daveho/FPGA_VGA/Schematic/FPGA_VGA.kicad_sch

## KiCad design Schematic/FPGA_VGA.kicad_sch (2025-11-19, an earlier design)

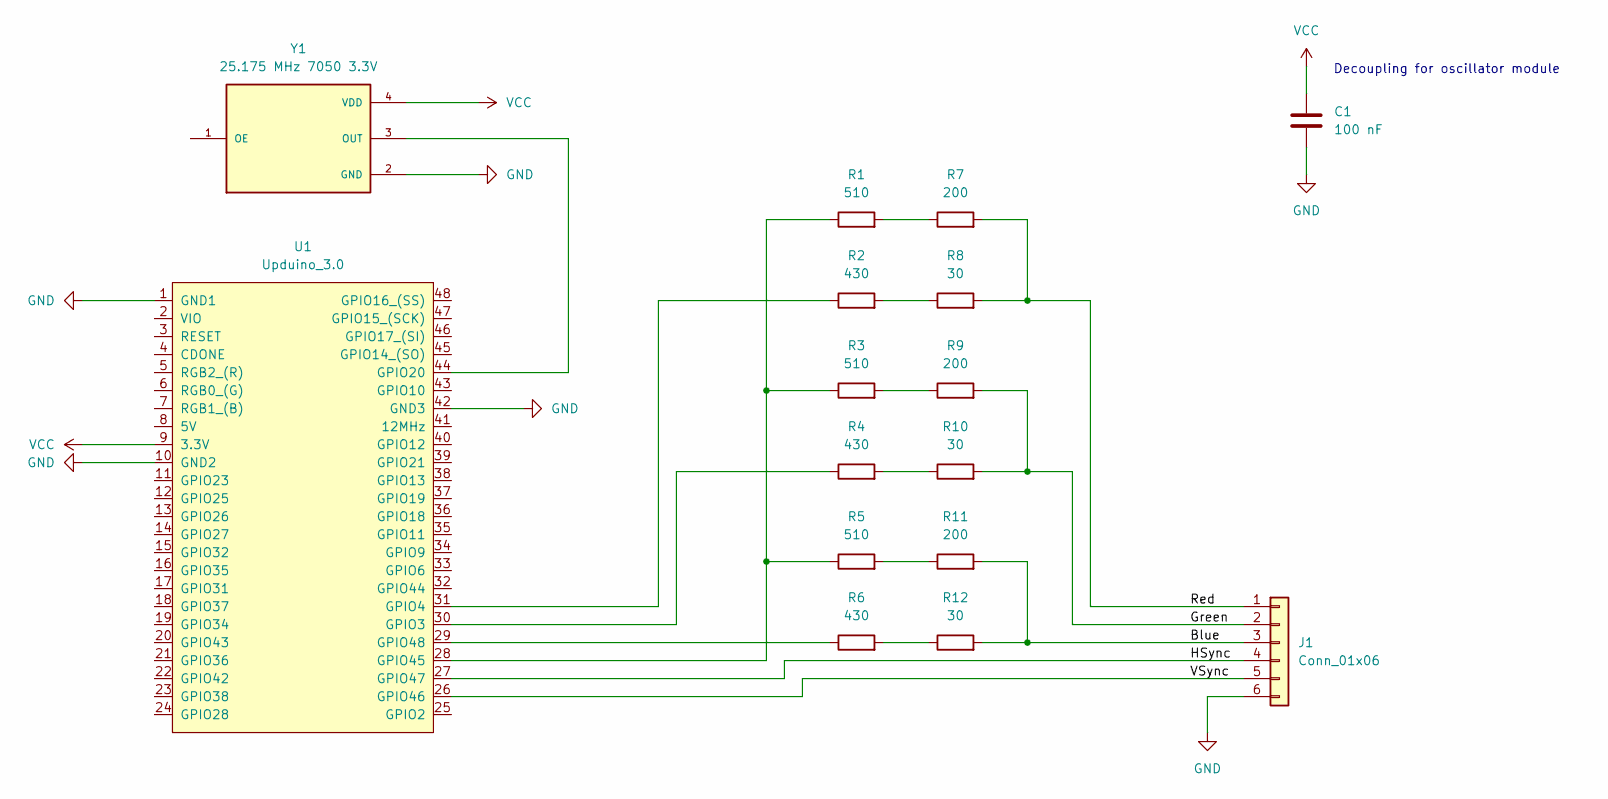
[picture p10: schematic FPGA_VGA.kicad_sch]

Parts:
C1: 100 nF
J1: Conn_01x06
R1, R3, R5: 510
R2, R4, R6: 430
R7, R9, R11: 200
R8, R10, R12: 30
U1: Upduino_3.0
Y1: 25.175 MHz 7050 3.3V; OSC_SIT8208AI-8F-33E-14.745600Y; PARTREV NA

Connections:
Blue: J1.3, R11.2, R12.2
GND: C1.2, J1.6, U1.1 (GND1), U1.10 (GND2), U1.42 (GND3), Y1.2 (GND)
Green: J1.2, R9.2, R10.2
HSync: J1.4, U1.27 (GPIO47)
unnamed: R1.1, R3.1, R5.1, U1.28 (GPIO45)
unnamed: R1.2, R7.1
unnamed: R2.1, U1.31 (GPIO4)
unnamed: R2.2, R8.1
unnamed: R3.2, R9.1
unnamed: R4.1, U1.30 (GPIO3)
unnamed: R6.1, U1.29 (GPIO48)
unnamed: R4.2, R10.1
unnamed: R5.2, R11.1
unnamed: R6.2, R12.1
unnamed: U1.44 (GPIO20), Y1.3 (OUT)
Red: J1.1, R7.2, R8.2
VCC: C1.1, U1.9 (3.3V), Y1.4 (VDD)
VSync: J1.5, U1.26 (GPIO46)

Notes on the sheet:
Decoupling for oscillator module
